siggy/bbox/docs/assets/images/bbox.playa.2018_1200.630.jpg

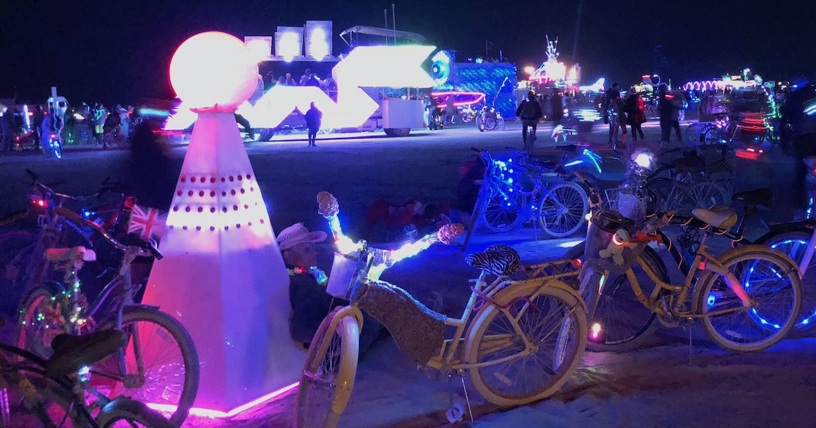
docs/assets/images/bbox.playa.2018_1200.630.jpg
