siggy/bbox/docs/assets/images/stake_drive.jpg

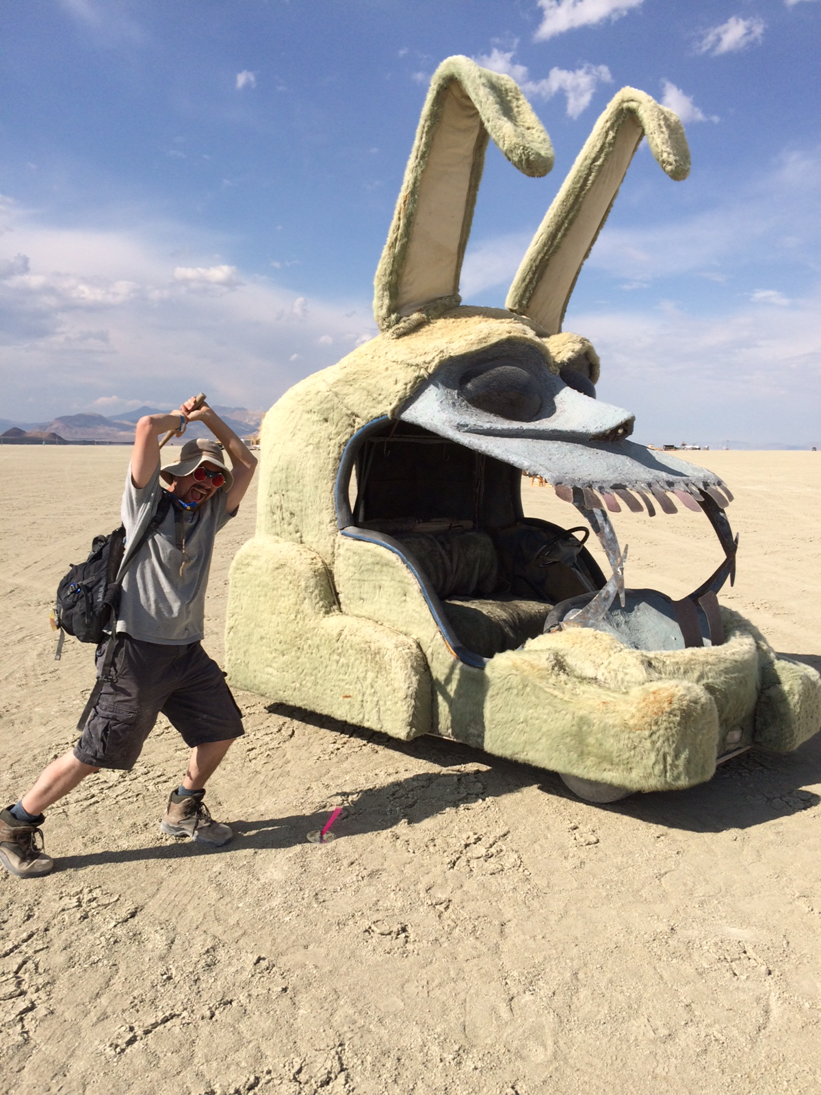
docs/assets/images/stake_drive.jpg
